VoronDesign/Voron-Switchwire/DXF/deck_panel_right.dxf

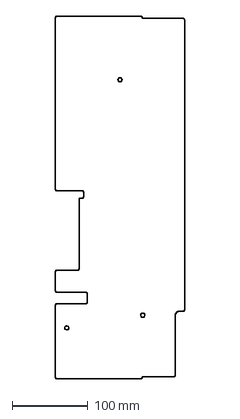
[picture p15: CAD file, 2020-08-28]
DXF/deck_panel_right.dxf
170.0 x 478.0 mm
