VoronDesign/Voron-Switchwire/STL/Electronics/LCD/2004_(Prusa)/lcd_case_rear_2004.stl

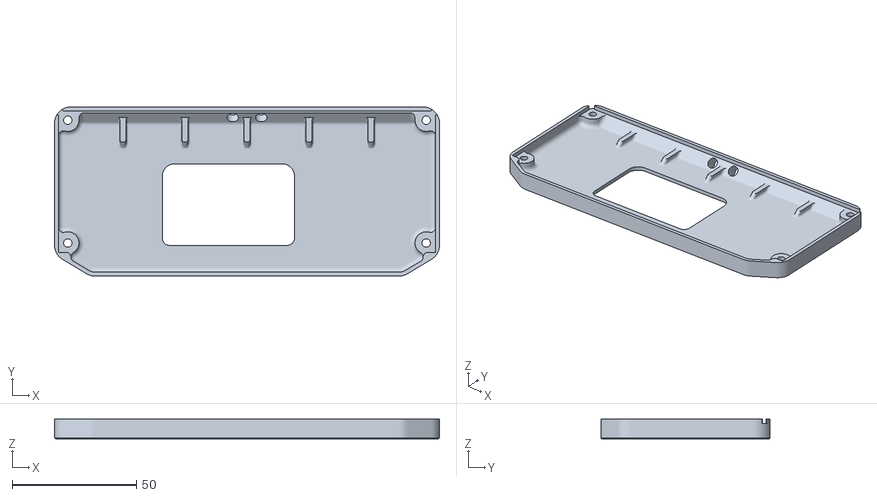
[picture p16: CAD file, 2020-08-08]
STL/Electronics/LCD/2004_(Prusa)/lcd_case_rear_2004.stl
155.2 x 68.2 x 8.00
