VoronDesign/Voron-Switchwire/STL/Electronics/LCD/Mini12864/lcd_case_rear_mini12864.stl

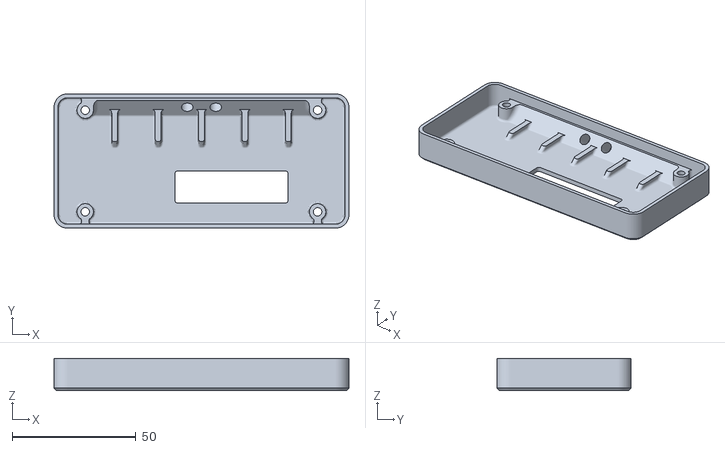
[picture p17: CAD file, 2020-08-08]
STL/Electronics/LCD/Mini12864/lcd_case_rear_mini12864.stl
119.0 x 54.2 x 13.0
