VoronDesign/Voron-Switchwire/STL/Electronics/skr_mount_rotated.stl

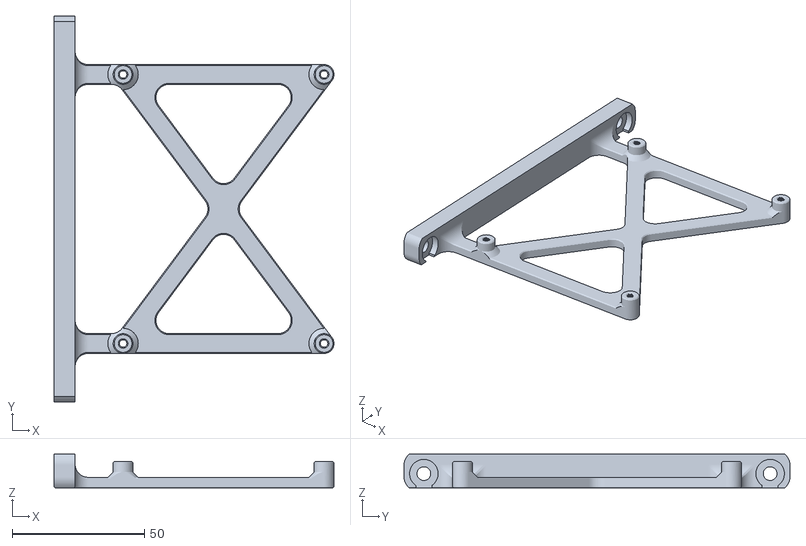
[picture p18: CAD file, 2020-12-18]
STL/Electronics/skr_mount_rotated.stl
106.0 x 146.1 x 12.8
