VoronDesign/Voron-Switchwire/STL/Gantry/3030_MGN12_guide_x2.stl

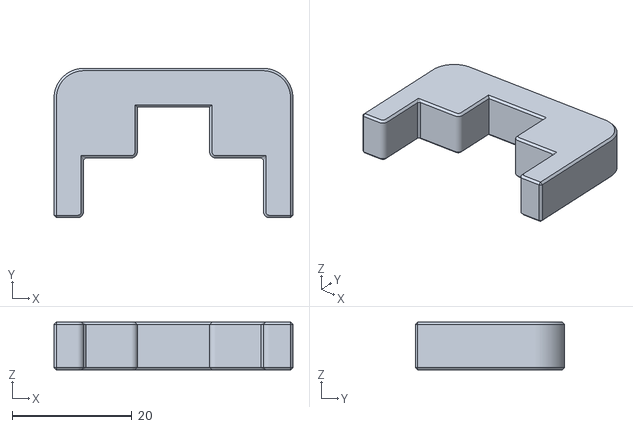
[picture p19: CAD file, 2020-08-08]
STL/Gantry/3030_MGN12_guide_x2.stl
40.0 x 25.0 x 8.00
