VoronDesign/Voron-Switchwire/STL/Gantry/Y_Axis/[a]_y_chain_frame_mount_igus.stl

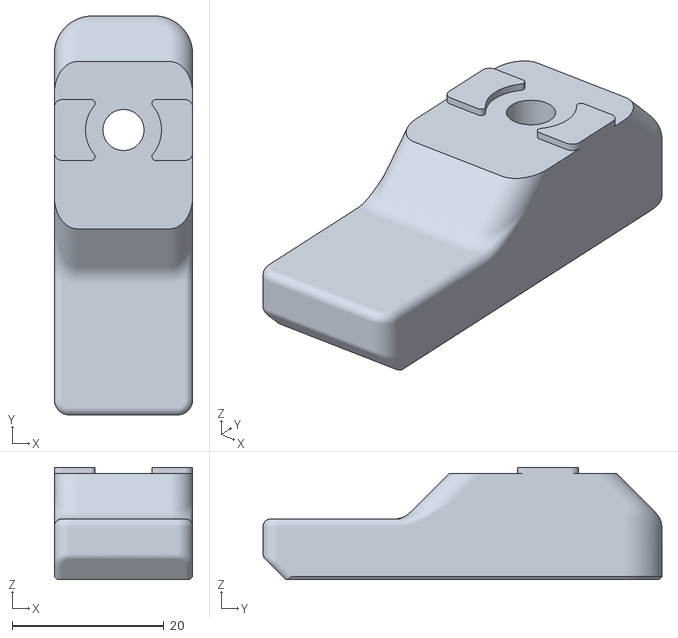
[picture p20: CAD file, 2020-12-18]
STL/Gantry/Y_Axis/[a]_y_chain_frame_mount_igus.stl
18.2 x 52.5 x 14.8
