VoronDesign/Voron-Switchwire/STL/Grills/[a]_grill_endcap_x4.stl

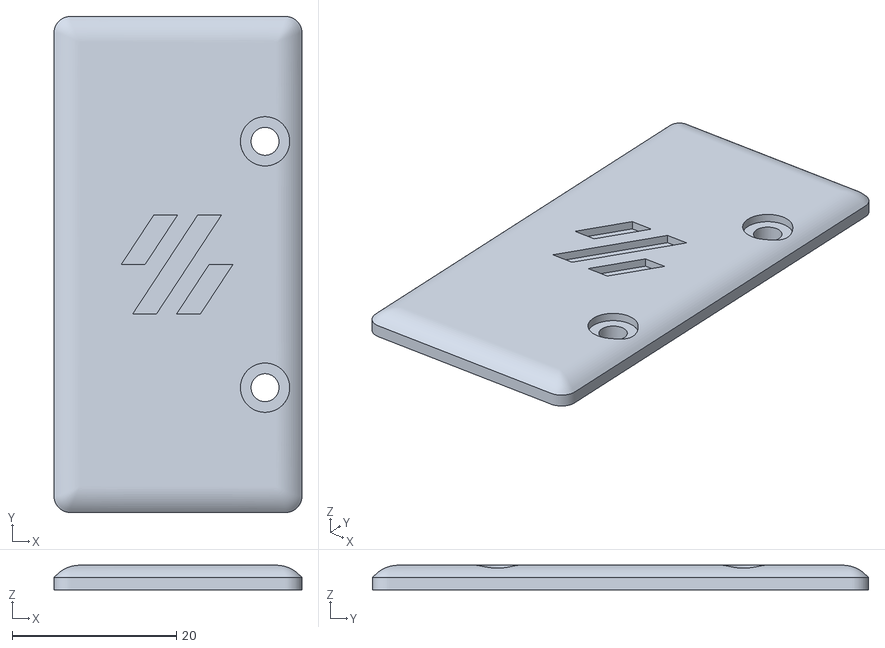
[picture p21: CAD file, 2020-08-08]
STL/Grills/[a]_grill_endcap_x4.stl
30.2 x 60.4 x 3.00
