VoronDesign/Voron-Switchwire/STL/Panel_Mounting/Doors/door_hinge_x4.stl

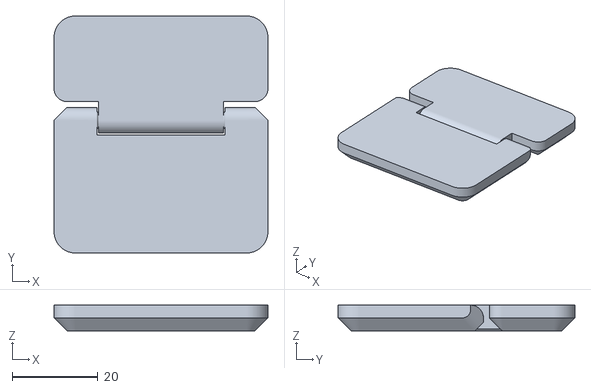
[picture p22: CAD file, 2020-08-08]
STL/Panel_Mounting/Doors/door_hinge_x4.stl
50.0 x 55.4 x 6.00
