VoronDesign/Voron-Switchwire/STL/Panel_Mounting/rear_panel_bracket_x6.stl

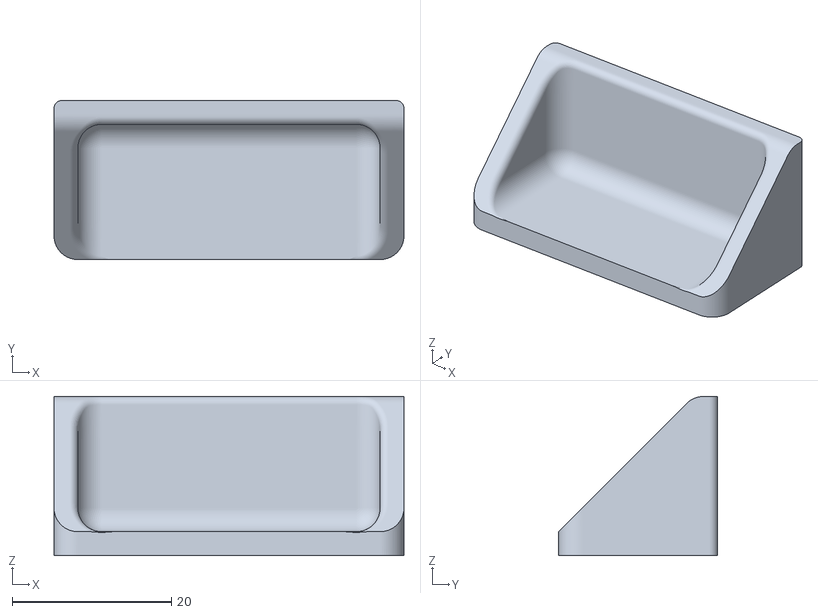
[picture p23: CAD file, 2020-08-08]
STL/Panel_Mounting/rear_panel_bracket_x6.stl
44.0 x 20.0 x 20.0
