VoronDesign/Voron-Switchwire/STL/spool_holder.stl

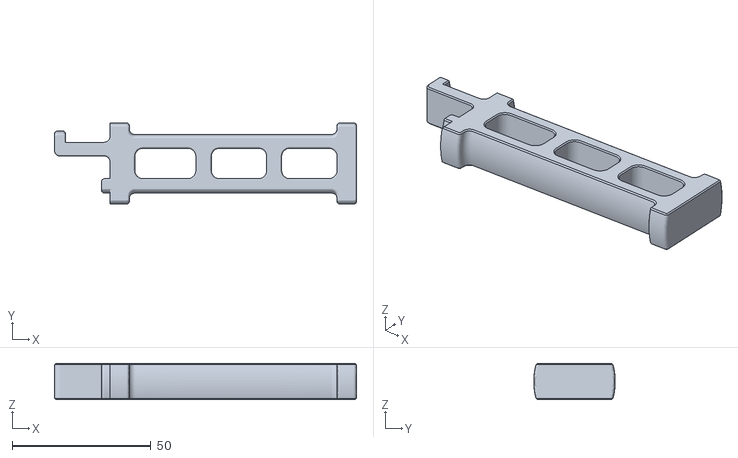
[picture p24: CAD file, 2020-08-08]
STL/spool_holder.stl
109.0 x 29.4 x 13.0
