VoronDesign/Voron-Switchwire/DXF/rear_panel_abs.dxf

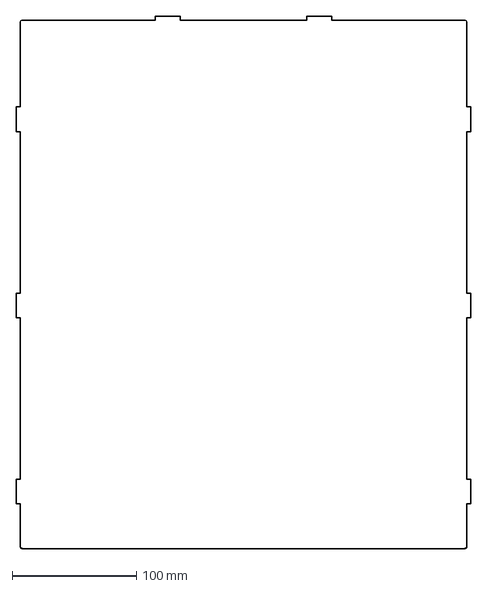
[picture p25: CAD file, 2020-08-28]
DXF/rear_panel_abs.dxf
366.0 x 429.0 mm
