VoronDesign/Voron-Switchwire/STL/Electronics/LCD/2004_(Prusa)/[a]_lcd_knob.stl

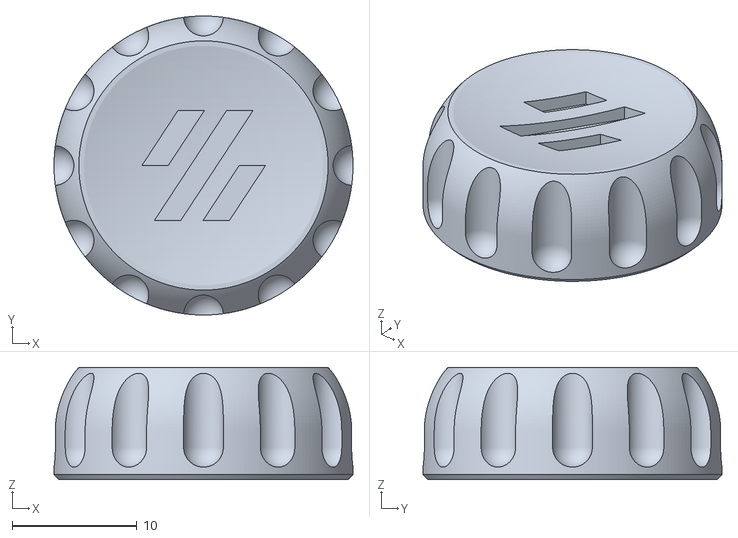
[picture p26: CAD file, 2020-08-08]
STL/Electronics/LCD/2004_(Prusa)/[a]_lcd_knob.stl
24.0 x 24.0 x 9.00
