VoronDesign/Voron-Switchwire/STL/Electronics/PS_3030_Mount_x2.stl

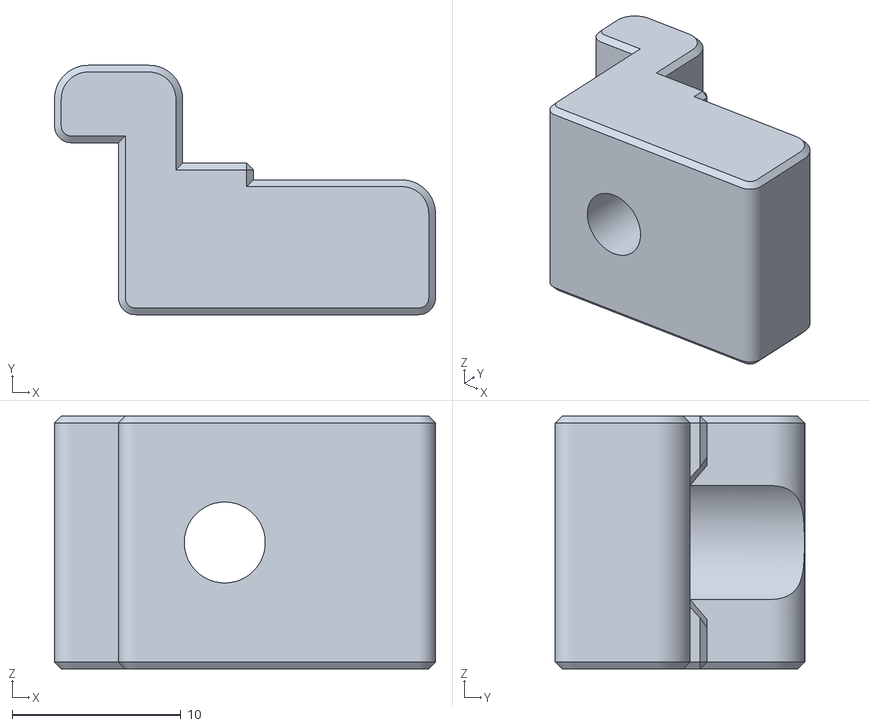
[picture p27: CAD file, 2020-08-08]
STL/Electronics/PS_3030_Mount_x2.stl
22.6 x 14.8 x 15.0
