VoronDesign/Voron-Switchwire/STL/Gantry/XZ_Axis/X_Carriage/[a]_x_bearing_block.stl

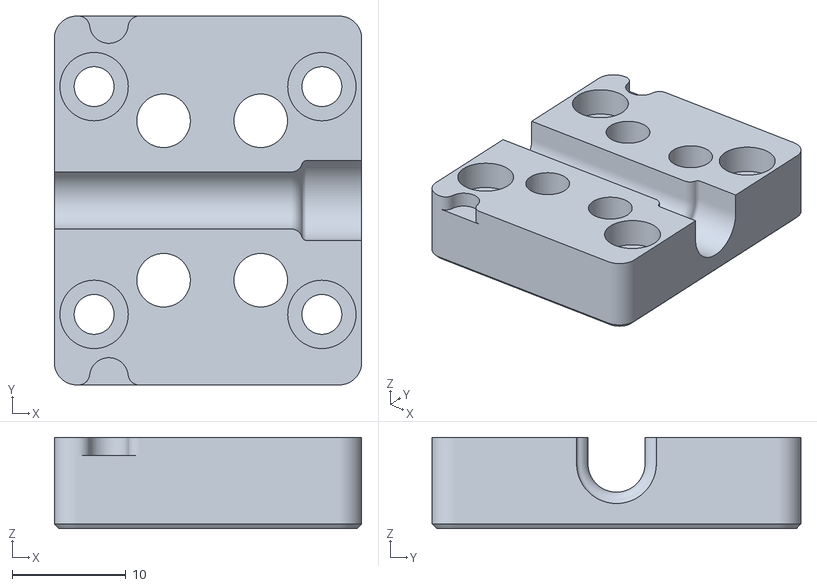
[picture p28: CAD file, 2020-08-08]
STL/Gantry/XZ_Axis/X_Carriage/[a]_x_bearing_block.stl
27.0 x 32.4 x 8.00
