VoronDesign/Voron-Switchwire/STL/Gantry/XZ_Axis/xz_block_right_a.stl

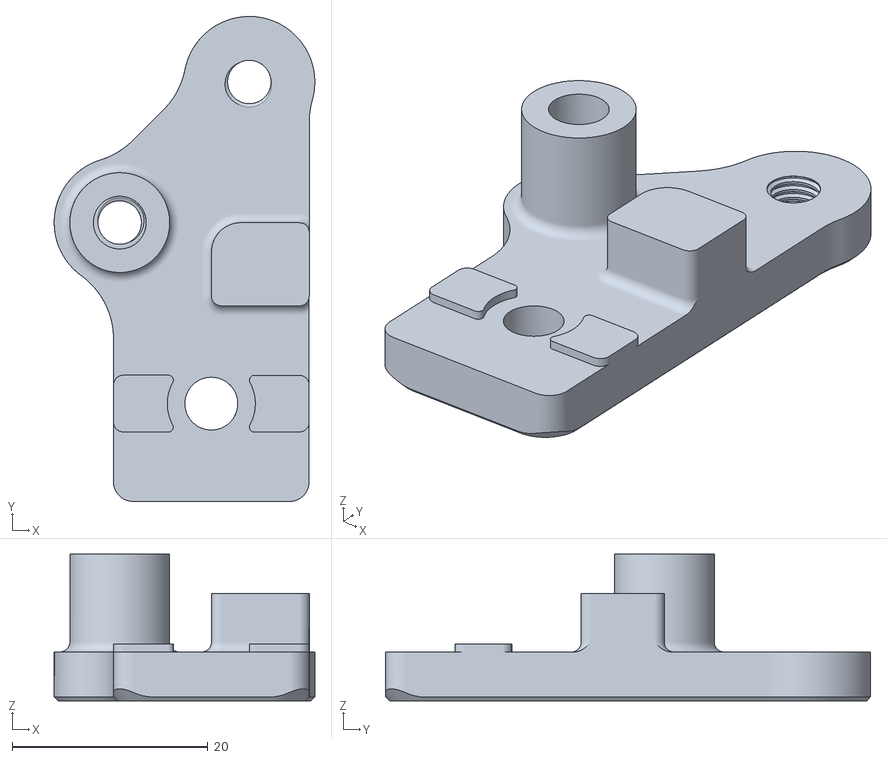
[picture p29: CAD file, 2020-08-28]
STL/Gantry/XZ_Axis/xz_block_right_a.stl
26.7 x 49.6 x 15.0
