VoronDesign/Voron-Switchwire/STL/Gantry/Y_Axis/[a]_y_chain_bed_mount_generic.stl

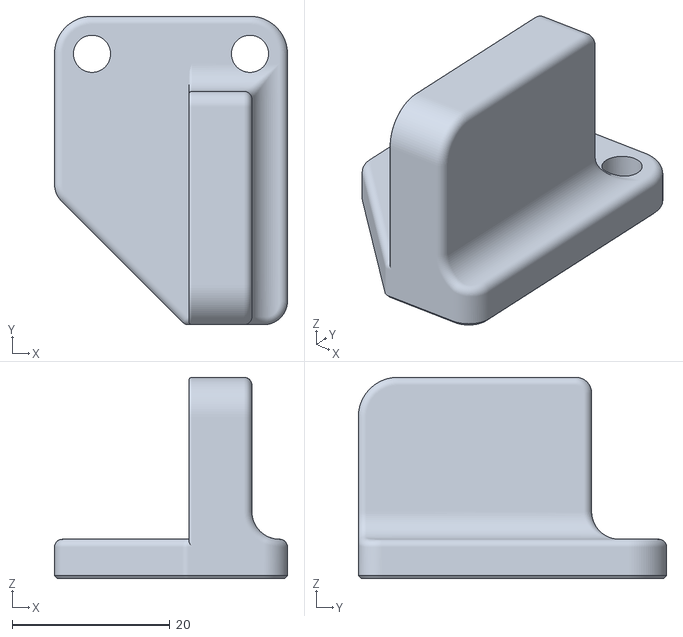
[picture p30: CAD file, 2020-12-18]
STL/Gantry/Y_Axis/[a]_y_chain_bed_mount_generic.stl
29.5 x 39.0 x 25.5
