VoronDesign/Voron-Switchwire/STL/Panel_Mounting/panel_clip_x10.stl

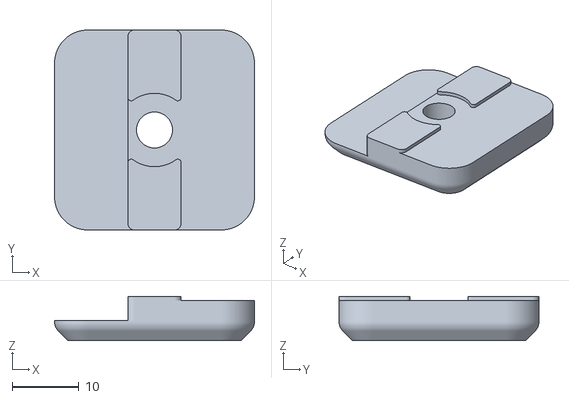
[picture p31: CAD file, 2020-08-08]
STL/Panel_Mounting/panel_clip_x10.stl
30.0 x 30.0 x 6.60
