VoronDesign/Voron-Switchwire/STL/spool_holder_base.stl

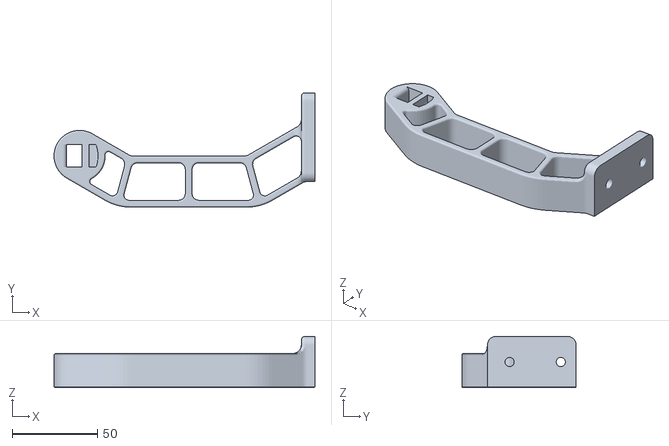
[picture p32: CAD file, 2020-08-08]
STL/spool_holder_base.stl
153.0 x 67.0 x 30.0
