VoronDesign/Voron-Switchwire/STL/Electronics/raspberry_pi_mount.stl

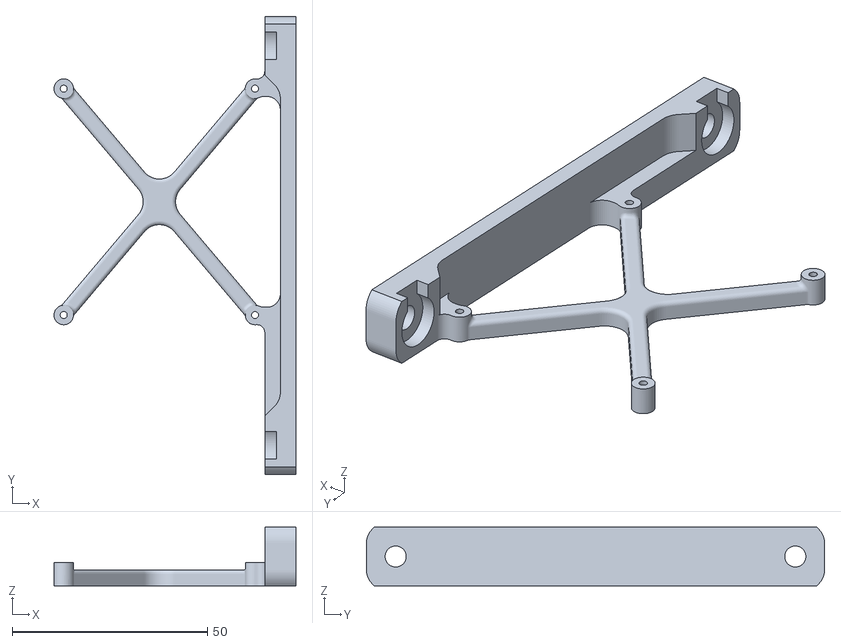
[picture p34: CAD file, 2020-08-08]
STL/Electronics/raspberry_pi_mount.stl
62.0 x 117.4 x 15.0
