VoronDesign/Voron-Switchwire/STL/Gantry/XZ_Axis/xz_block_left_a.stl

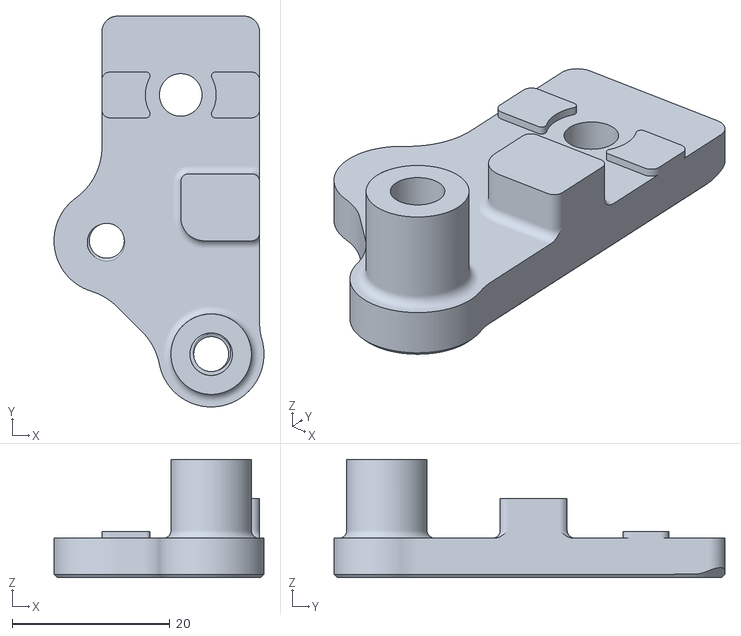
[picture p35: CAD file, 2020-08-28]
STL/Gantry/XZ_Axis/xz_block_left_a.stl
26.6 x 49.6 x 15.0
