VoronDesign/Voron-Switchwire/STL/Grills/grill_front_middle.stl

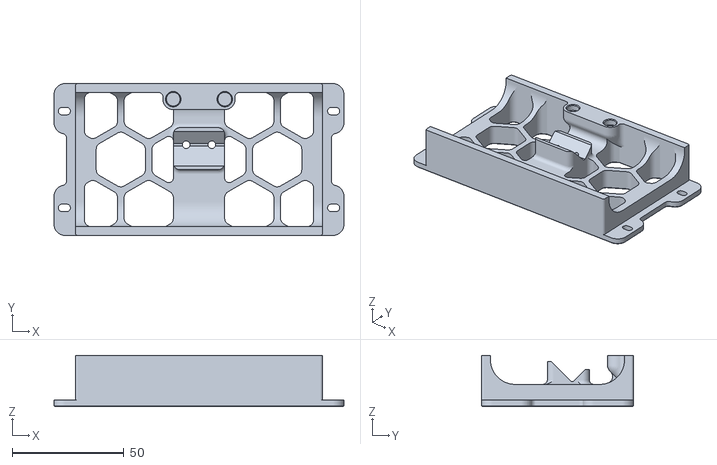
[picture p36: CAD file, 2020-08-08]
STL/Grills/grill_front_middle.stl
129.8 x 68.0 x 23.0
