VoronDesign/Voron-Switchwire/STL/Panel_Mounting/light_bar_x2.stl

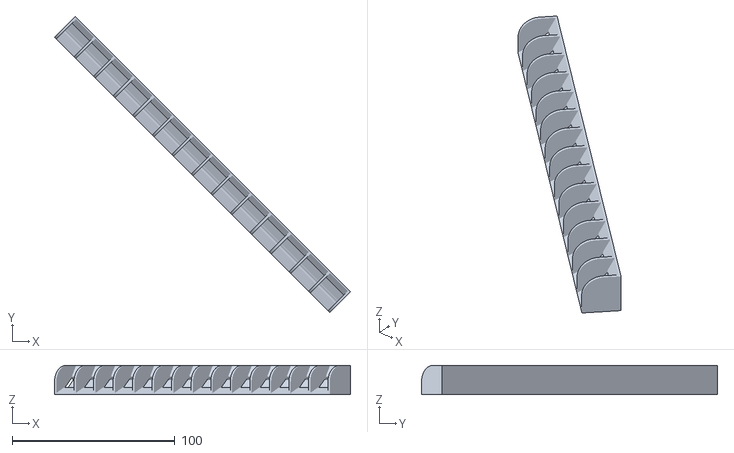
[picture p37: CAD file, 2020-08-08]
STL/Panel_Mounting/light_bar_x2.stl
182.2 x 182.2 x 18.0
