VoronDesign/Voron-Switchwire/DXF/side_panel_left_abs.dxf

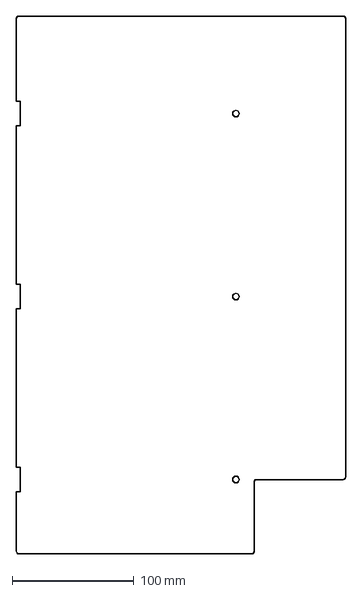
[picture p38: CAD file, 2020-08-28]
DXF/side_panel_left_abs.dxf
270.0 x 441.0 mm
