VoronDesign/Voron-Switchwire/STL/Electronics/raspberry_pi_zero_shelf.stl

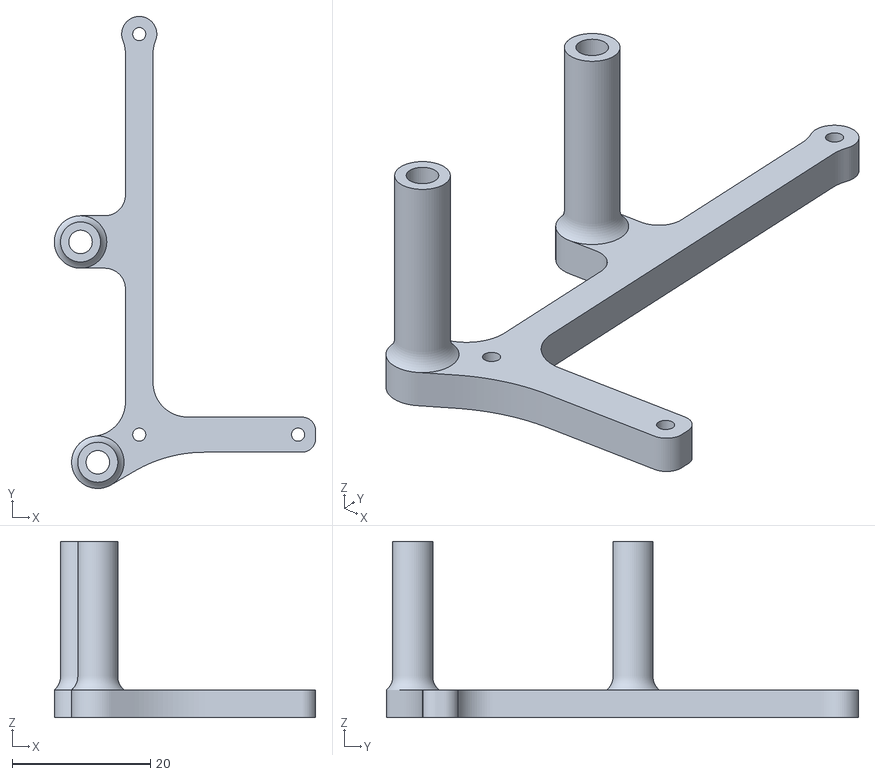
[picture p39: CAD file, 2020-08-08]
STL/Electronics/raspberry_pi_zero_shelf.stl
37.8 x 68.3 x 25.5
