VoronDesign/Voron-Switchwire/STL/Gantry/XZ_Axis/upper_idler_support_a_right.stl

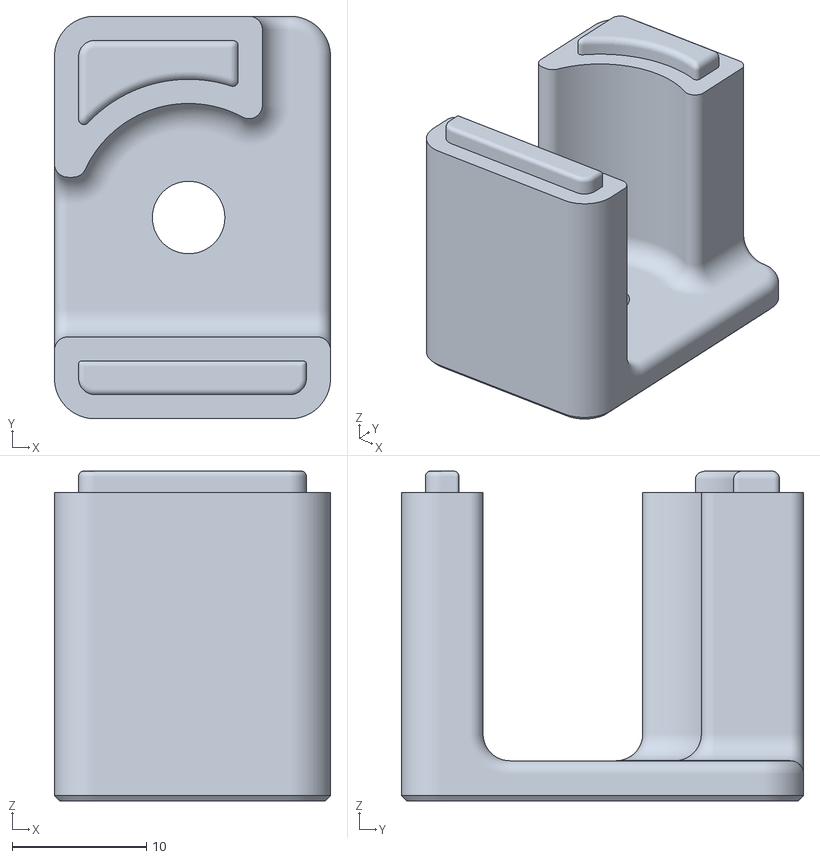
[picture p40: CAD file, 2020-08-08]
STL/Gantry/XZ_Axis/upper_idler_support_a_right.stl
20.6 x 30.0 x 24.6
