VoronDesign/Voron-Switchwire/STL/Gantry/XZ_Axis/X_Carriage/[a]_xz_belt_clip_x2.stl

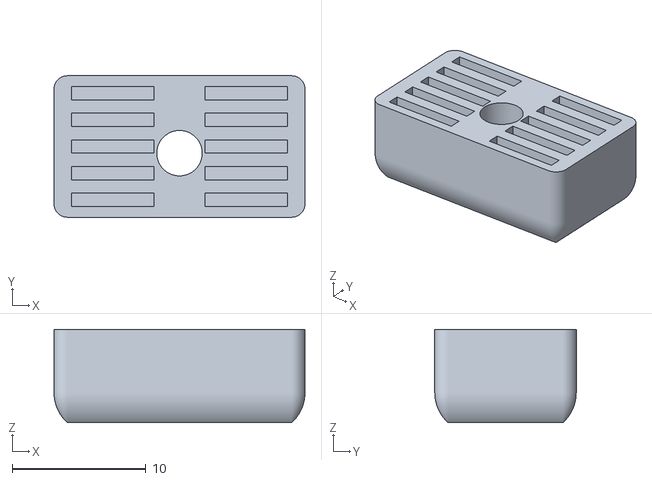
[picture p41: CAD file, 2020-08-08]
STL/Gantry/XZ_Axis/X_Carriage/[a]_xz_belt_clip_x2.stl
18.8 x 10.6 x 7.00
