VoronDesign/Voron-Switchwire/STL/Gantry/Y_Axis/[a]_dummy_microswitch.stl

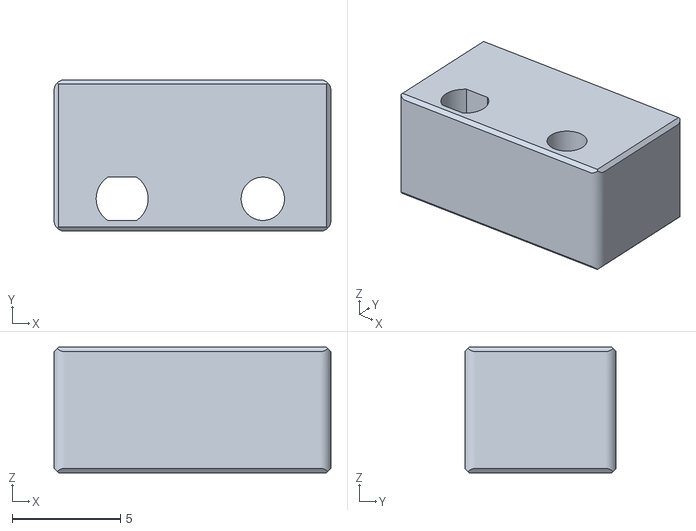
[picture p42: CAD file, 2020-12-18]
STL/Gantry/Y_Axis/[a]_dummy_microswitch.stl
12.8 x 7.00 x 5.80
