VoronDesign/Voron-Switchwire/STL/Grills/grill_rear_middle.stl

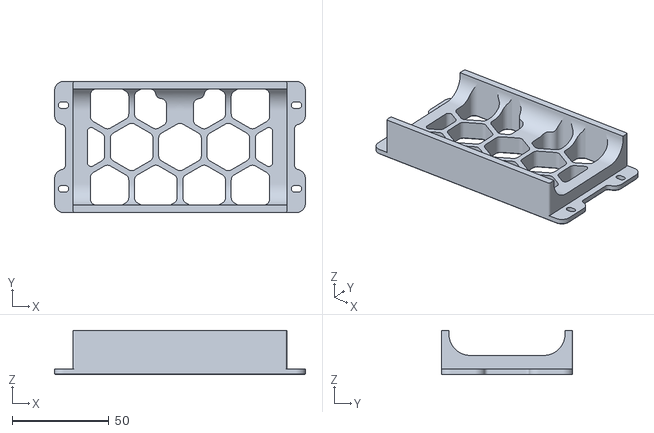
[picture p43: CAD file, 2020-08-08]
STL/Grills/grill_rear_middle.stl
129.8 x 68.0 x 23.0
