VoronDesign/Voron-Switchwire/STL/Panel_Mounting/top_door_latch.stl

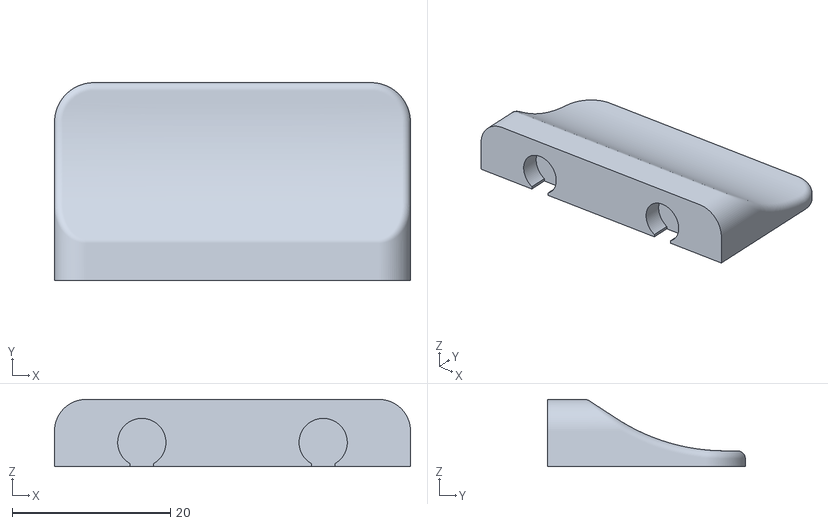
[picture p44: CAD file, 2020-08-08]
STL/Panel_Mounting/top_door_latch.stl
45.0 x 25.0 x 8.50
