VoronDesign/Voron-Switchwire/DXF/side_panel_left.dxf

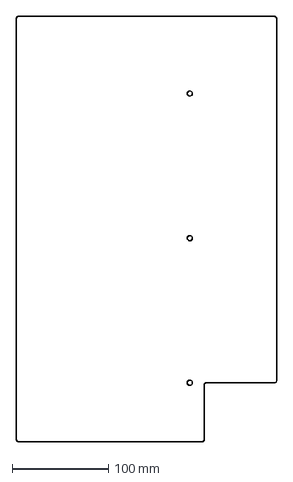
[picture p45: CAD file, 2020-08-08]
DXF/side_panel_left.dxf
270.0 x 441.0 mm
