VoronDesign/Voron-Switchwire/STL/Electronics/3030_wire_clip.stl

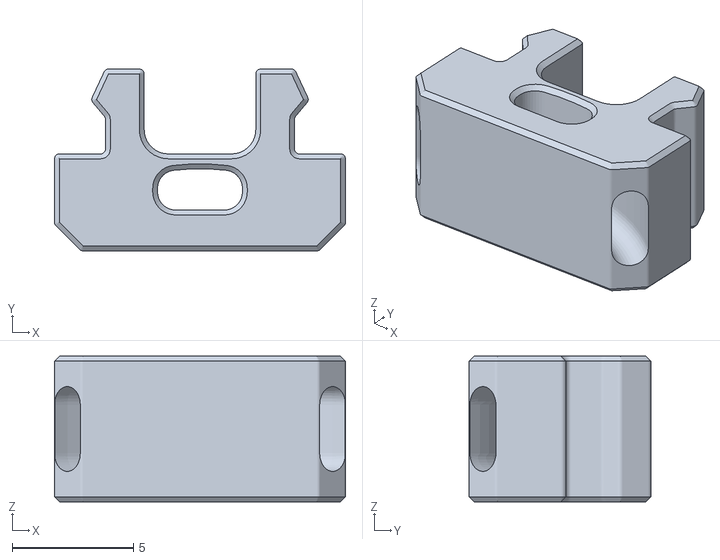
[picture p46: CAD file, 2020-08-08]
STL/Electronics/3030_wire_clip.stl
12.0 x 7.50 x 6.00
