VoronDesign/Voron-Switchwire/STL/Gantry/XZ_Axis/keybak_idler_bracket.stl

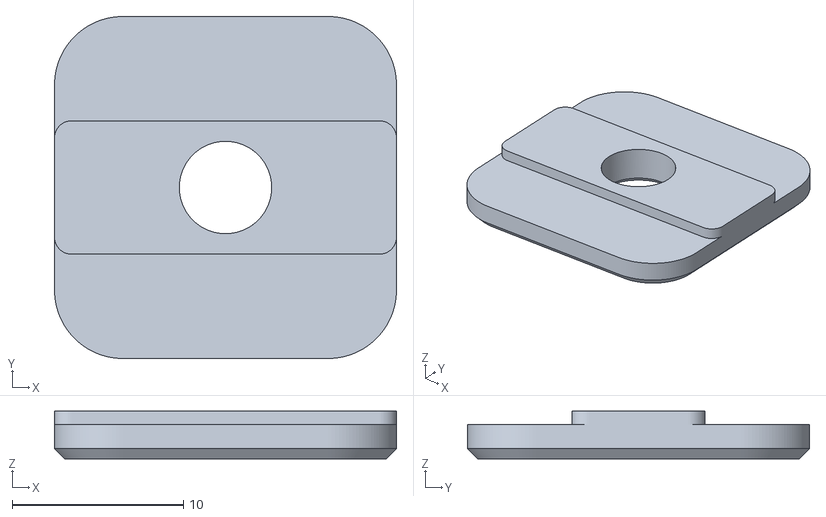
[picture p47: CAD file, 2020-08-08]
STL/Gantry/XZ_Axis/keybak_idler_bracket.stl
20.0 x 20.0 x 2.80
