VoronDesign/Voron-Switchwire/STL/Gantry/XZ_Axis/X_Carriage/probe_retainer_bracket.stl

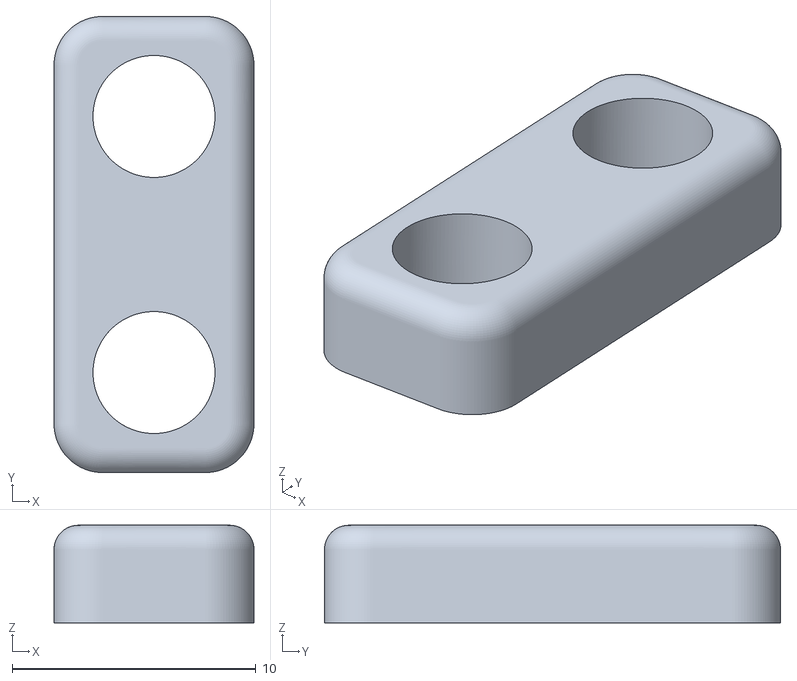
[picture p48: CAD file, 2020-08-08]
STL/Gantry/XZ_Axis/X_Carriage/probe_retainer_bracket.stl
8.20 x 18.7 x 4.00
