VoronDesign/Voron-Switchwire/STL/Grills/grill_rear_right.stl

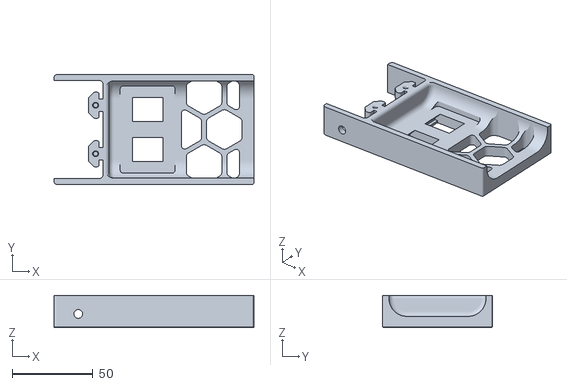
[picture p49: CAD file, 2020-08-08]
STL/Grills/grill_rear_right.stl
123.7 x 68.0 x 20.0
