VoronDesign/Voron-Switchwire/STL/Panel_Mounting/feed_slot.stl

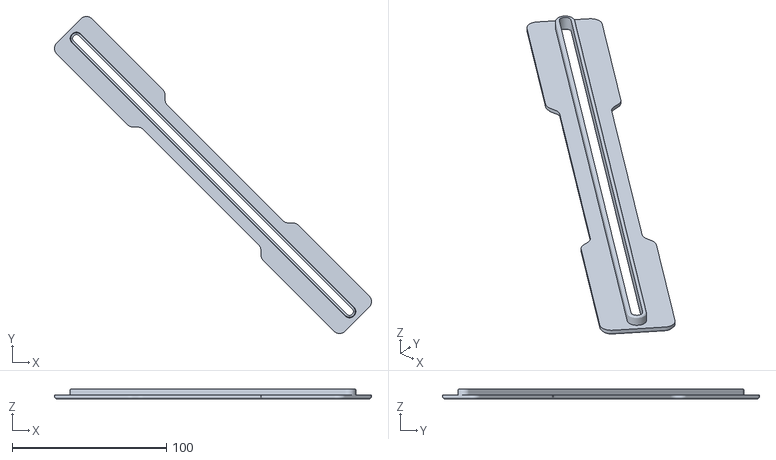
[picture p50: CAD file, 2020-08-08]
STL/Panel_Mounting/feed_slot.stl
205.3 x 205.3 x 6.40
