VoronDesign/Voron-Switchwire/DXF/top_panel.dxf

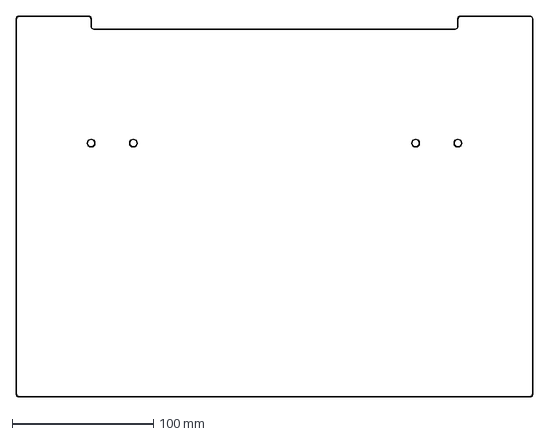
[picture p51: CAD file, 2020-08-08]
DXF/top_panel.dxf
366.0 x 270.0 mm
