VoronDesign/Voron-Switchwire/STL/Electronics/PS_2020_Mount_x2.stl

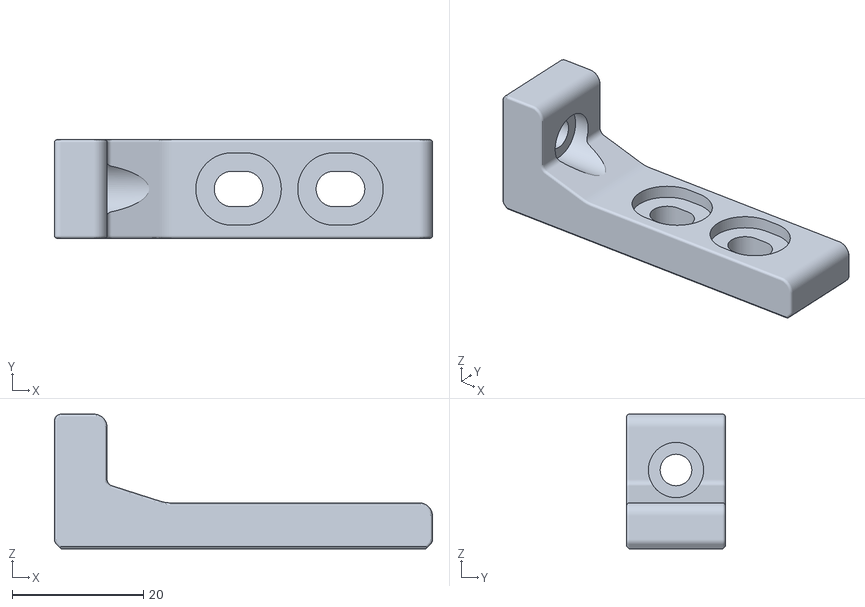
[picture p52: CAD file, 2020-08-08]
STL/Electronics/PS_2020_Mount_x2.stl
57.5 x 15.0 x 20.5
