VoronDesign/Voron-Switchwire/STL/Gantry/XZ_Axis/[a]_upper_idler_support_b_right.stl

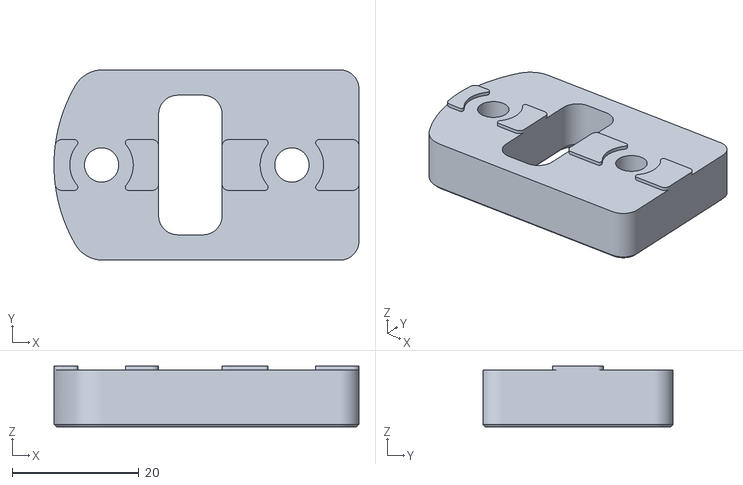
[picture p53: CAD file, 2020-08-08]
STL/Gantry/XZ_Axis/[a]_upper_idler_support_b_right.stl
48.1 x 30.0 x 9.60
