VoronDesign/Voron-Switchwire/STL/Gantry/Y_Axis/y_belt_anchor.stl

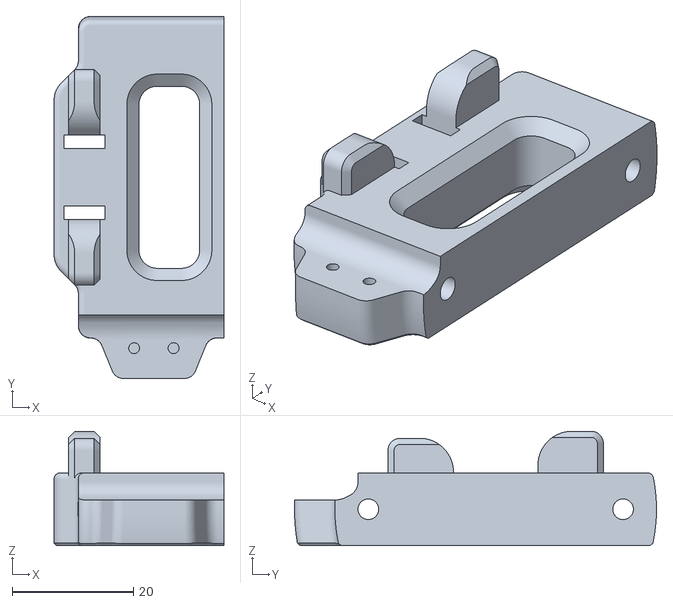
[picture p54: CAD file, 2020-08-28]
STL/Gantry/Y_Axis/y_belt_anchor.stl
28.0 x 59.7 x 18.8
