VoronDesign/Voron-Switchwire/DXF/deck_panel_left.dxf

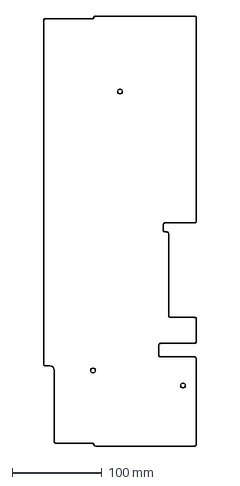
[picture p55: CAD file, 2020-08-08]
DXF/deck_panel_left.dxf
170.0 x 478.0 mm
