VoronDesign/Voron-Switchwire/STL/Electronics/einsy_rambo_mount.stl

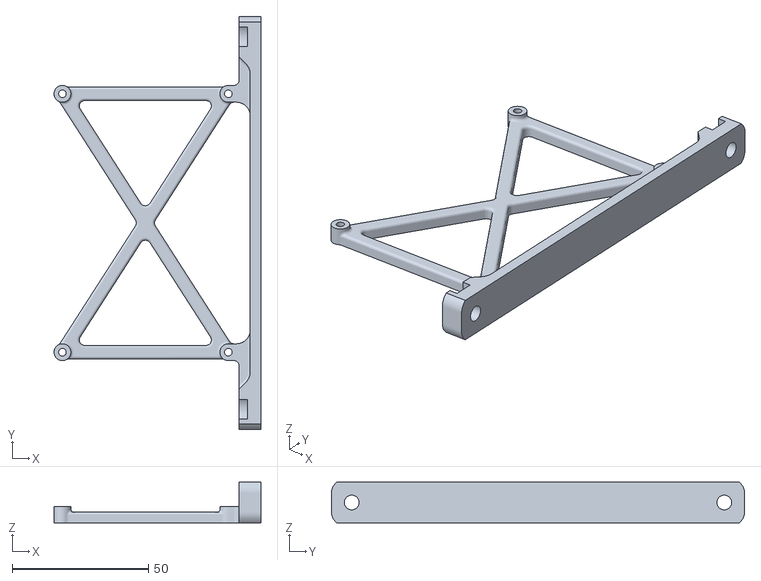
[picture p56: CAD file, 2020-08-08]
STL/Electronics/einsy_rambo_mount.stl
76.1 x 152.0 x 15.0
