VoronDesign/Voron-Switchwire/STL/Gantry/XZ_Axis/[a]_xz_cable_cover.stl

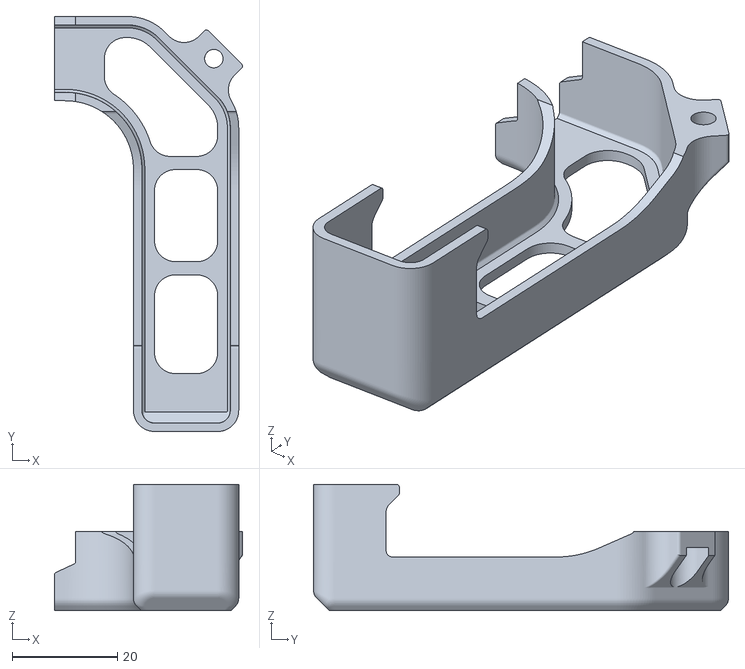
[picture p57: CAD file, 2020-08-08]
STL/Gantry/XZ_Axis/[a]_xz_cable_cover.stl
35.7 x 78.8 x 24.0
