VoronDesign/Voron-Switchwire/STL/Gantry/Y_Axis/heatbed_terminals_cover.stl

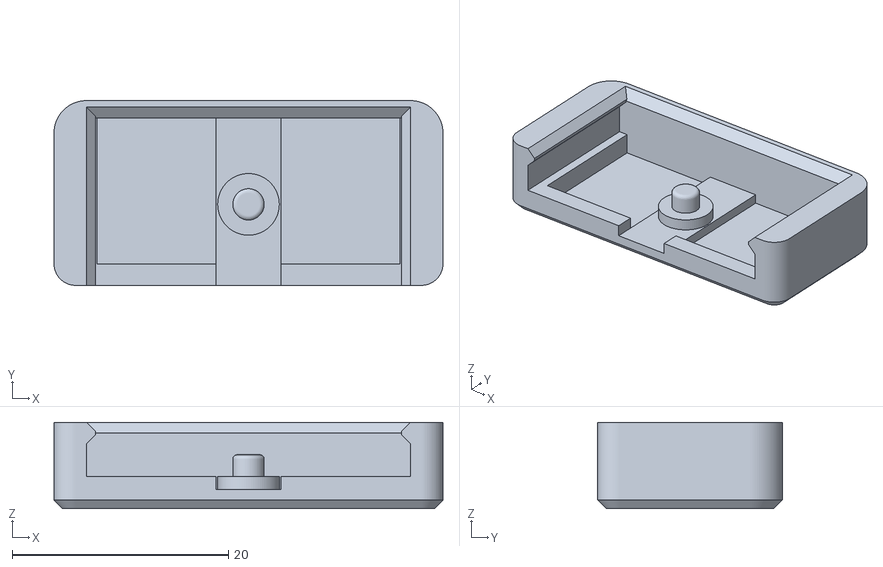
[picture p58: CAD file, 2020-08-10]
STL/Gantry/Y_Axis/heatbed_terminals_cover.stl
36.0 x 17.1 x 8.00
