VoronDesign/Voron-Switchwire/DXF/bottom_panel.dxf

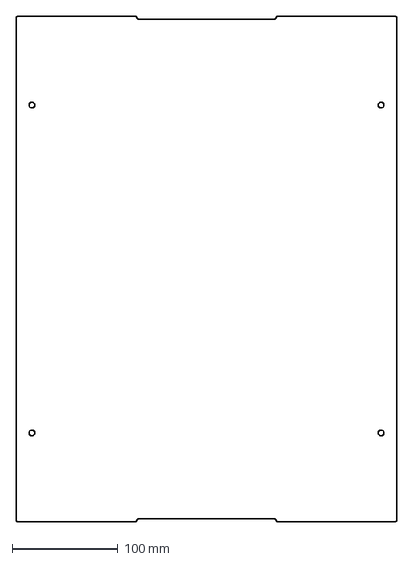
[picture p59: CAD file, 2020-08-08]
DXF/bottom_panel.dxf
360.0 x 478.0 mm
