VoronDesign/Voron-Switchwire/STL/Electronics/rs_25_mount.stl

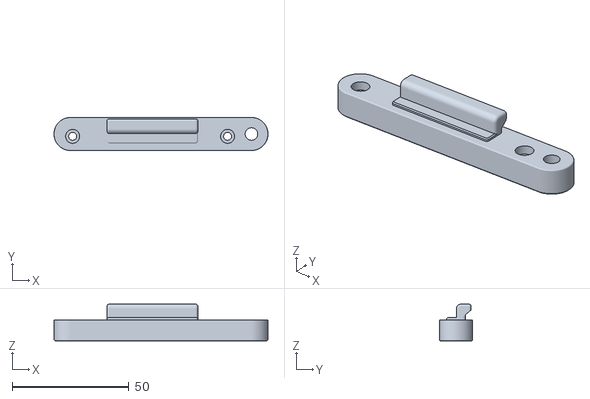
[picture p60: CAD file, 2020-08-08]
STL/Electronics/rs_25_mount.stl
91.9 x 14.2 x 15.8
