VoronDesign/Voron-Switchwire/STL/Gantry/Y_Axis/y_motor_mount_a.stl

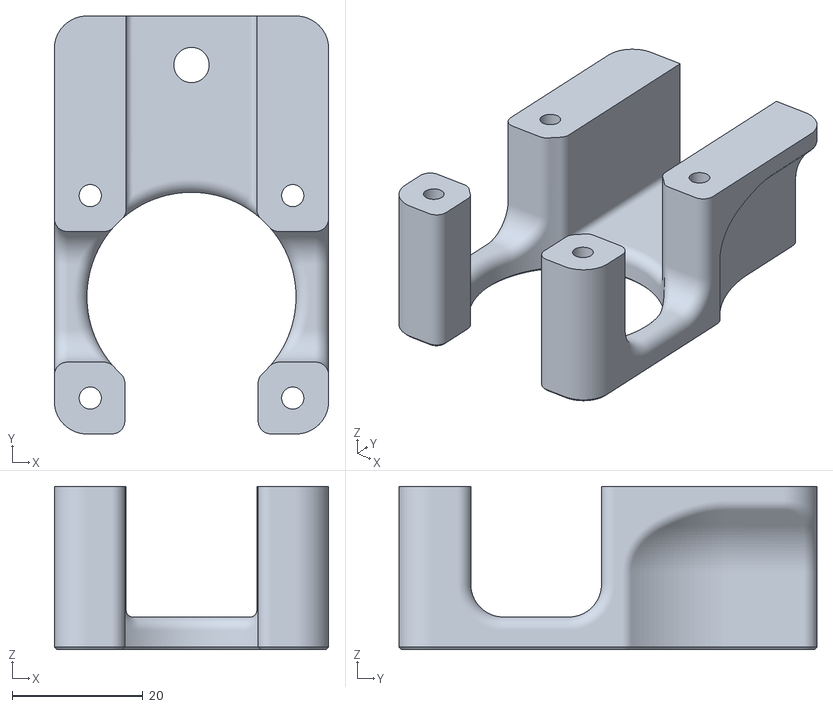
[picture p62: CAD file, 2020-08-08]
STL/Gantry/Y_Axis/y_motor_mount_a.stl
42.0 x 64.0 x 25.0
