VoronDesign/Voron-Switchwire/DXF/rear_panel.dxf

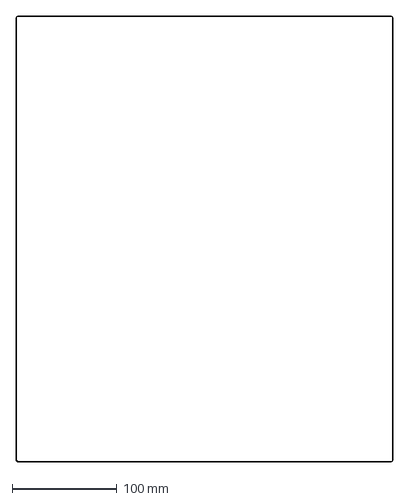
[picture p63: CAD file, 2020-08-08]
DXF/rear_panel.dxf
360.0 x 426.0 mm
