VoronDesign/Voron-Switchwire/STL/Electronics/skr_mini_e3_mount.stl

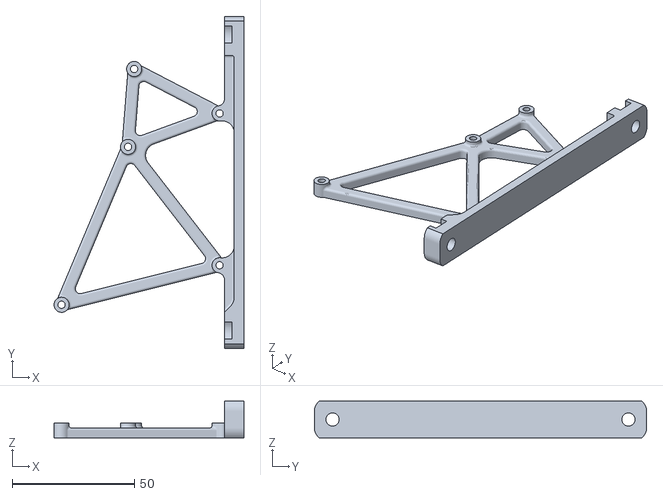
[picture p64: CAD file, 2020-08-08]
STL/Electronics/skr_mini_e3_mount.stl
77.8 x 136.2 x 15.0
