VoronDesign/Voron-Switchwire/STL/Gantry/XZ_Axis/z_bearing_block_left.stl

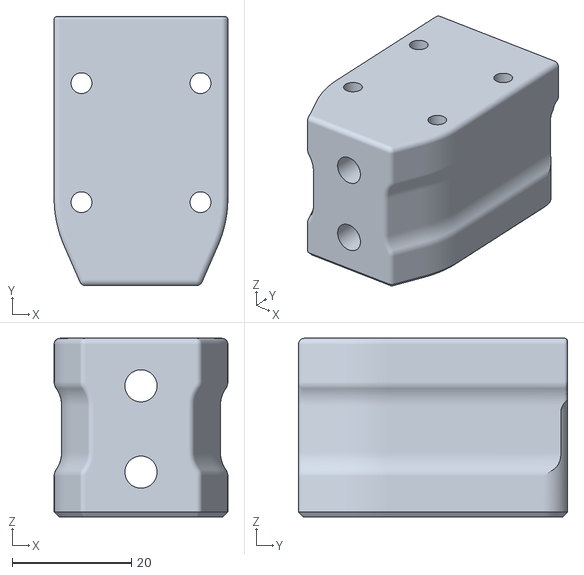
[picture p65: CAD file, 2020-08-08]
STL/Gantry/XZ_Axis/z_bearing_block_left.stl
29.2 x 45.2 x 30.0
