VoronDesign/Voron-Switchwire/STL/Gantry/Y_Axis/y_carriage_drill_guide.stl

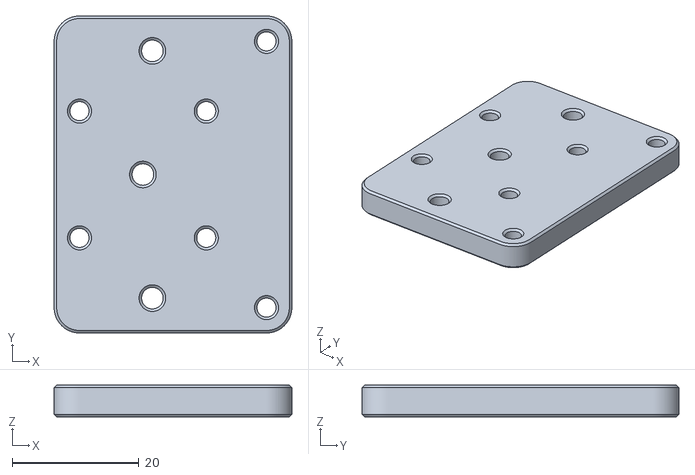
[picture p66: CAD file, 2020-08-08]
STL/Gantry/Y_Axis/y_carriage_drill_guide.stl
37.5 x 50.0 x 5.00
