VoronDesign/Voron-Switchwire/DXF/side_panel_right.dxf

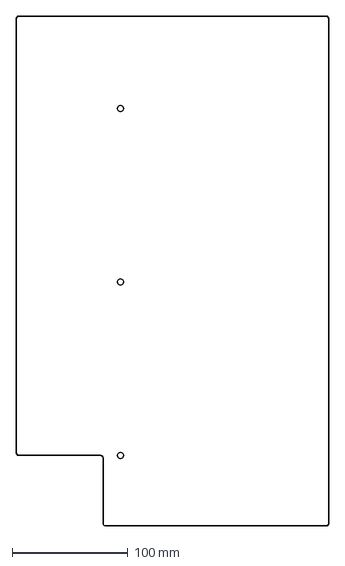
[picture p67: CAD file, 2020-08-08]
DXF/side_panel_right.dxf
270.0 x 441.0 mm
