VoronDesign/Voron-Switchwire/STL/Gantry/Y_Axis/y_motor_mount_b.stl

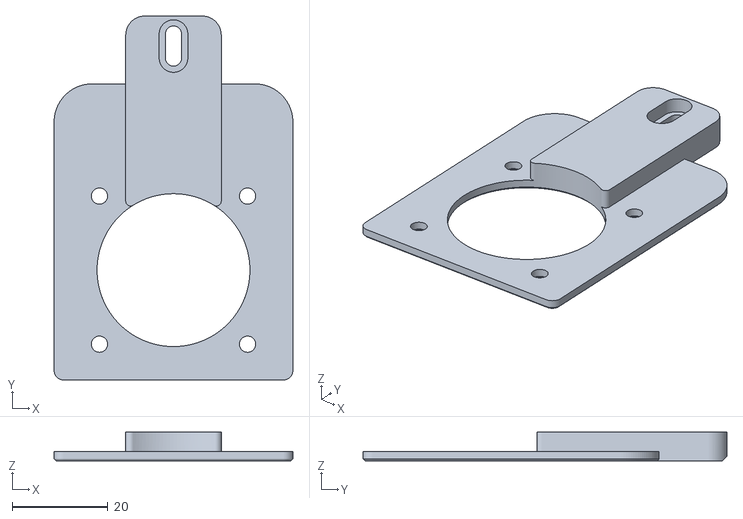
[picture p69: CAD file, 2020-08-08]
STL/Gantry/Y_Axis/y_motor_mount_b.stl
50.0 x 76.2 x 6.00
