VoronDesign/Voron-Switchwire/STL/Gantry/Y_Axis/[a]_y_belt_clip.stl

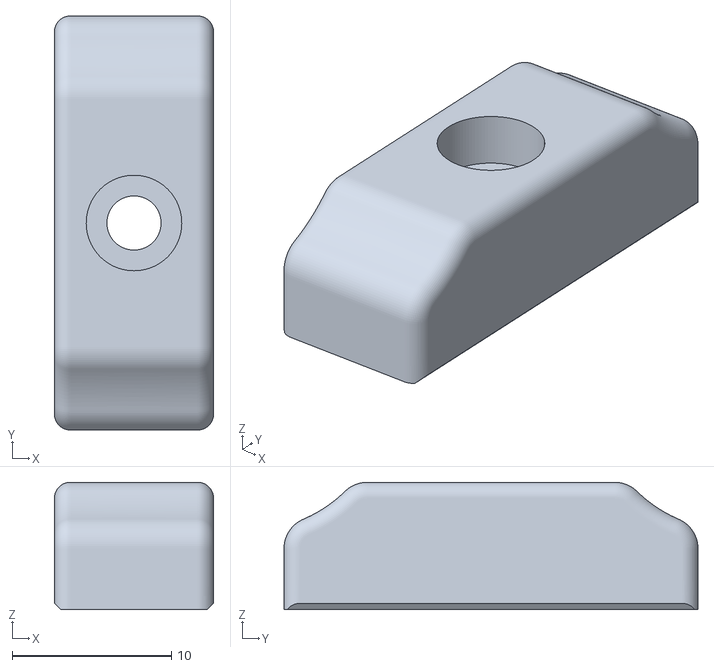
[picture p70: CAD file, 2020-08-08]
STL/Gantry/Y_Axis/[a]_y_belt_clip.stl
10.0 x 26.0 x 8.00
