VoronDesign/Voron-Switchwire/STL/Gantry/XZ_Axis/keybak_mount.stl

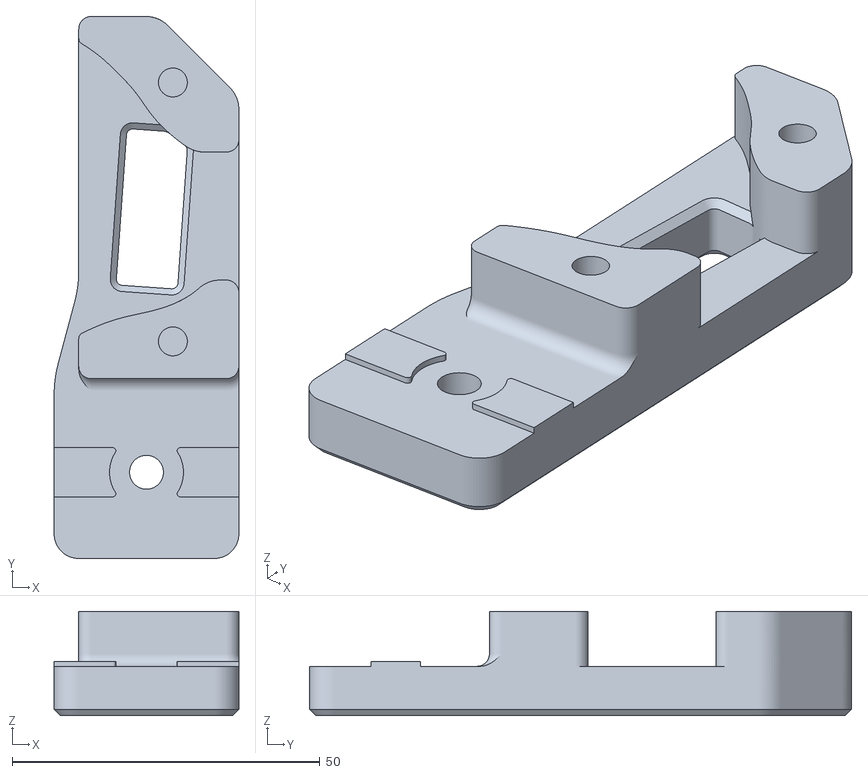
[picture p71: CAD file, 2020-08-08]
STL/Gantry/XZ_Axis/keybak_mount.stl
30.0 x 88.0 x 16.9
