VoronDesign/Voron-Switchwire/STL/Gantry/Y_Axis/y_idler_lower.stl

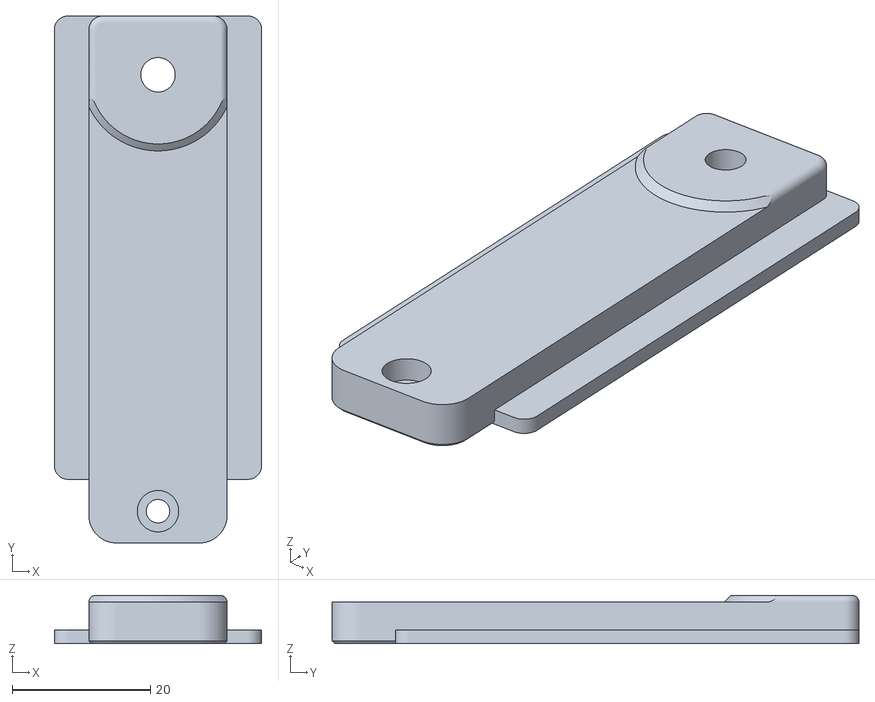
[picture p72: CAD file, 2020-08-08]
STL/Gantry/Y_Axis/y_idler_lower.stl
30.0 x 76.2 x 7.00
