VoronDesign/Voron-Switchwire/STL/Gantry/XZ_Axis/x_motor_mount_b.stl

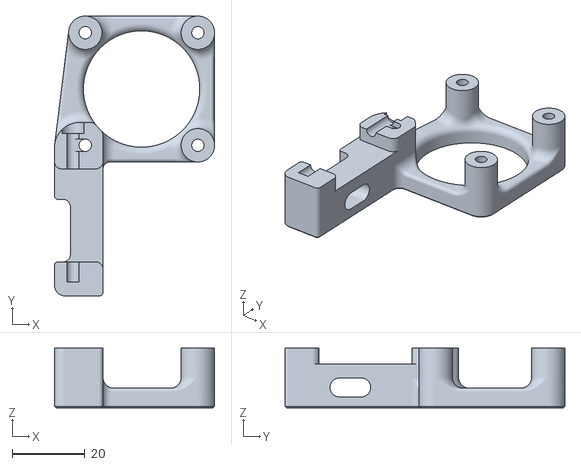
[picture p73: CAD file, 2020-08-08]
STL/Gantry/XZ_Axis/x_motor_mount_b.stl
44.1 x 77.1 x 16.4
