VoronDesign/Voron-Switchwire/STL/Gantry/Y_Axis/y_idler_upper.stl

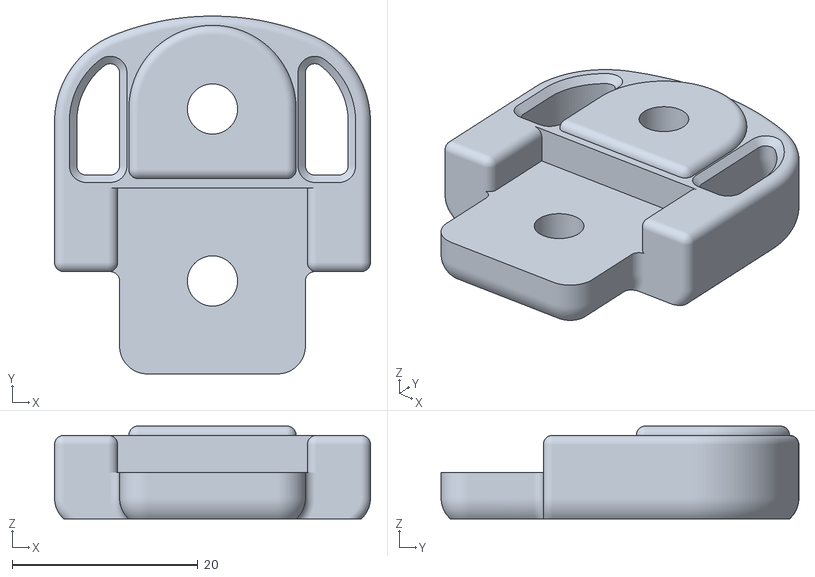
[picture p74: CAD file, 2020-08-08]
STL/Gantry/Y_Axis/y_idler_upper.stl
34.0 x 38.5 x 10.0
