VoronDesign/Voron-Switchwire/STL/Gantry/XZ_Axis/z_carriage_stop_x3.stl

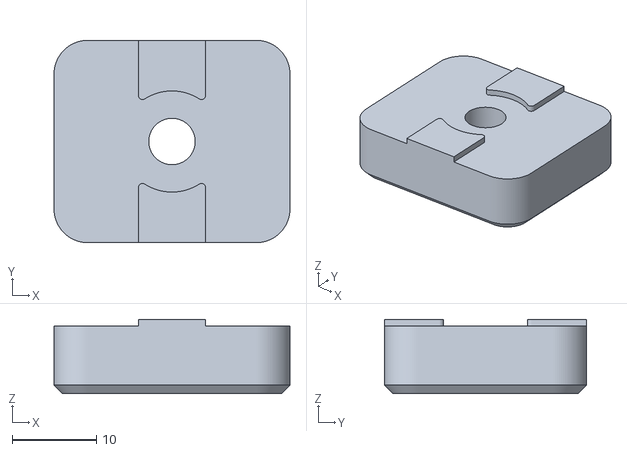
[picture p75: CAD file, 2020-08-08]
STL/Gantry/XZ_Axis/z_carriage_stop_x3.stl
28.0 x 24.0 x 8.80
