VoronDesign/Voron-Switchwire/STL/Gantry/XZ_Axis/z_bearing_block_right_igus.stl

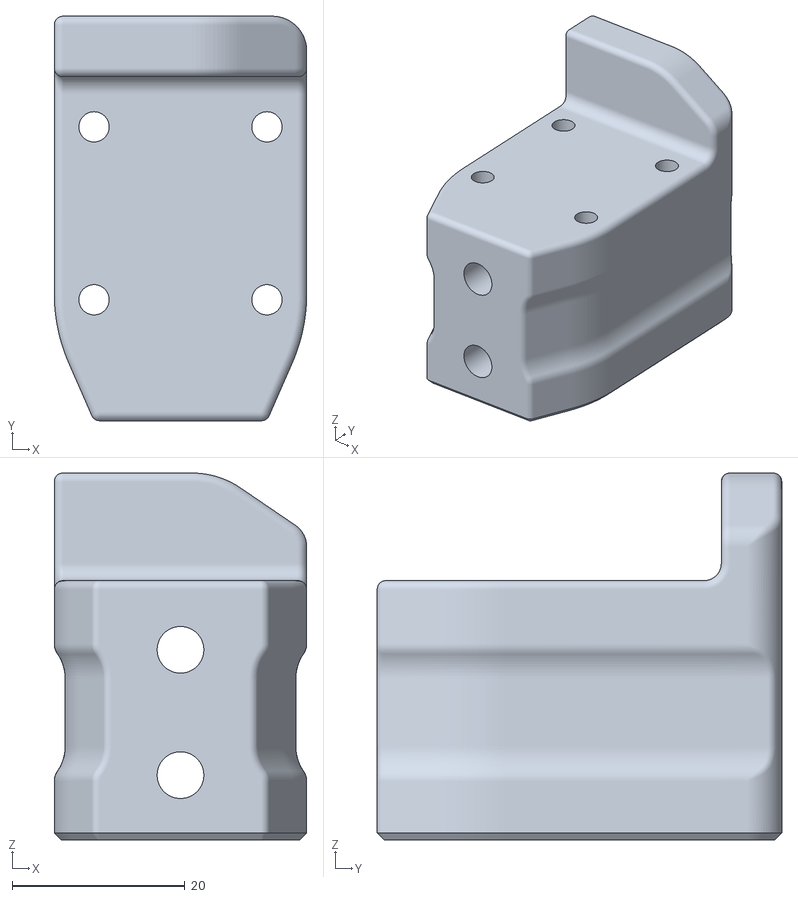
[picture p76: CAD file, 2020-08-08]
STL/Gantry/XZ_Axis/z_bearing_block_right_igus.stl
29.2 x 46.8 x 42.4
