VoronDesign/Voron-Switchwire/STL/Gantry/XZ_Axis/[a]_z_chain_lower_mount_generic.stl

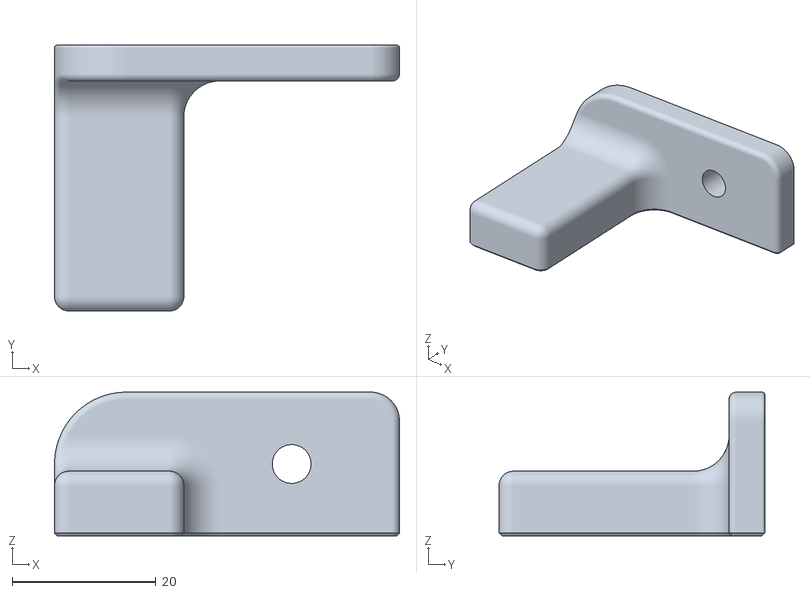
[picture p77: CAD file, 2020-08-08]
STL/Gantry/XZ_Axis/[a]_z_chain_lower_mount_generic.stl
48.0 x 37.0 x 20.0
