VoronDesign/Voron-Switchwire/STL/Gantry/XZ_Axis/keybak_gantry_anchor.stl

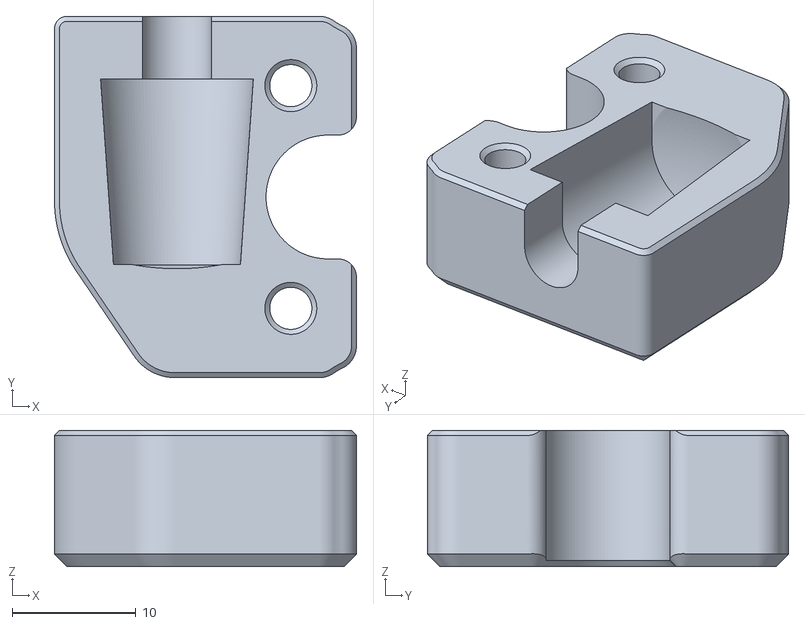
[picture p78: CAD file, 2020-08-08]
STL/Gantry/XZ_Axis/keybak_gantry_anchor.stl
24.4 x 29.2 x 11.0
