VoronDesign/Voron-Switchwire/STL/Gantry/XZ_Axis/keybak_mount_plate.stl

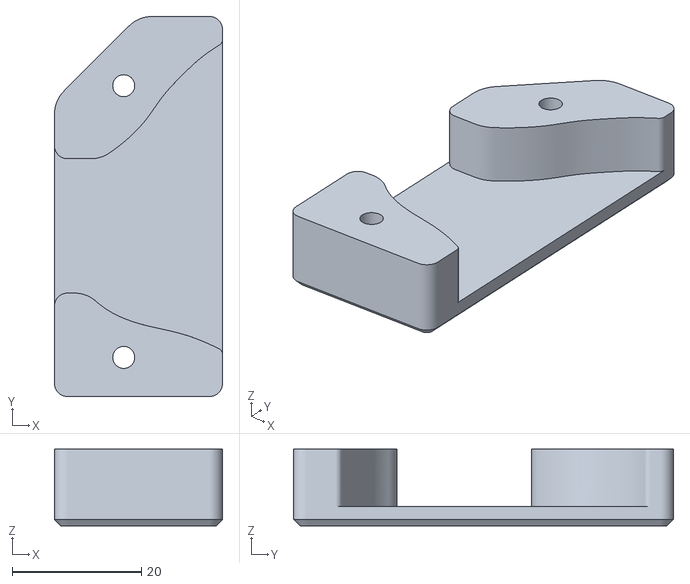
[picture p79: CAD file, 2020-08-08]
STL/Gantry/XZ_Axis/keybak_mount_plate.stl
26.0 x 58.8 x 11.9
