VoronDesign/Voron-Switchwire/STL/Gantry/XZ_Axis/[a]_xz_tensioner_x2.stl

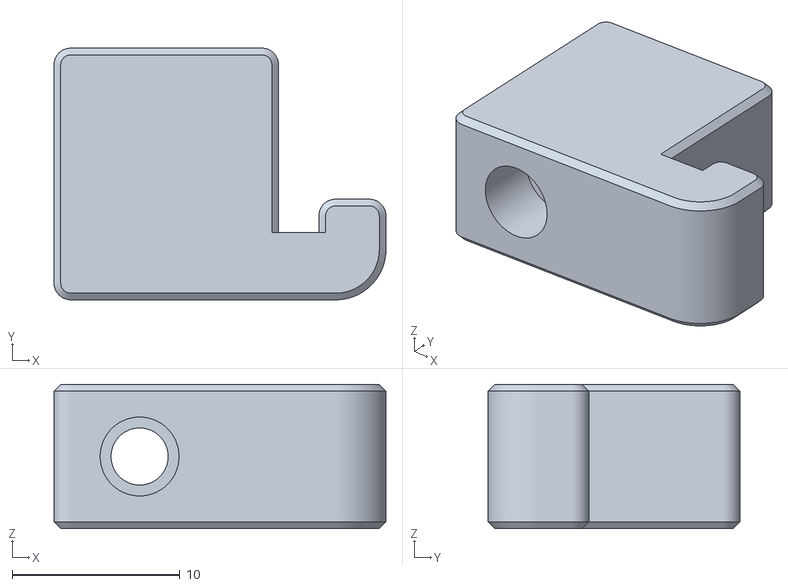
[picture p80: CAD file, 2020-08-08]
STL/Gantry/XZ_Axis/[a]_xz_tensioner_x2.stl
19.8 x 15.0 x 8.60
